myak555/EALIOR_Keyboard/Layout_Russian_Standard/ENGLISH_CAPS_Layout_Russian_Standard.png

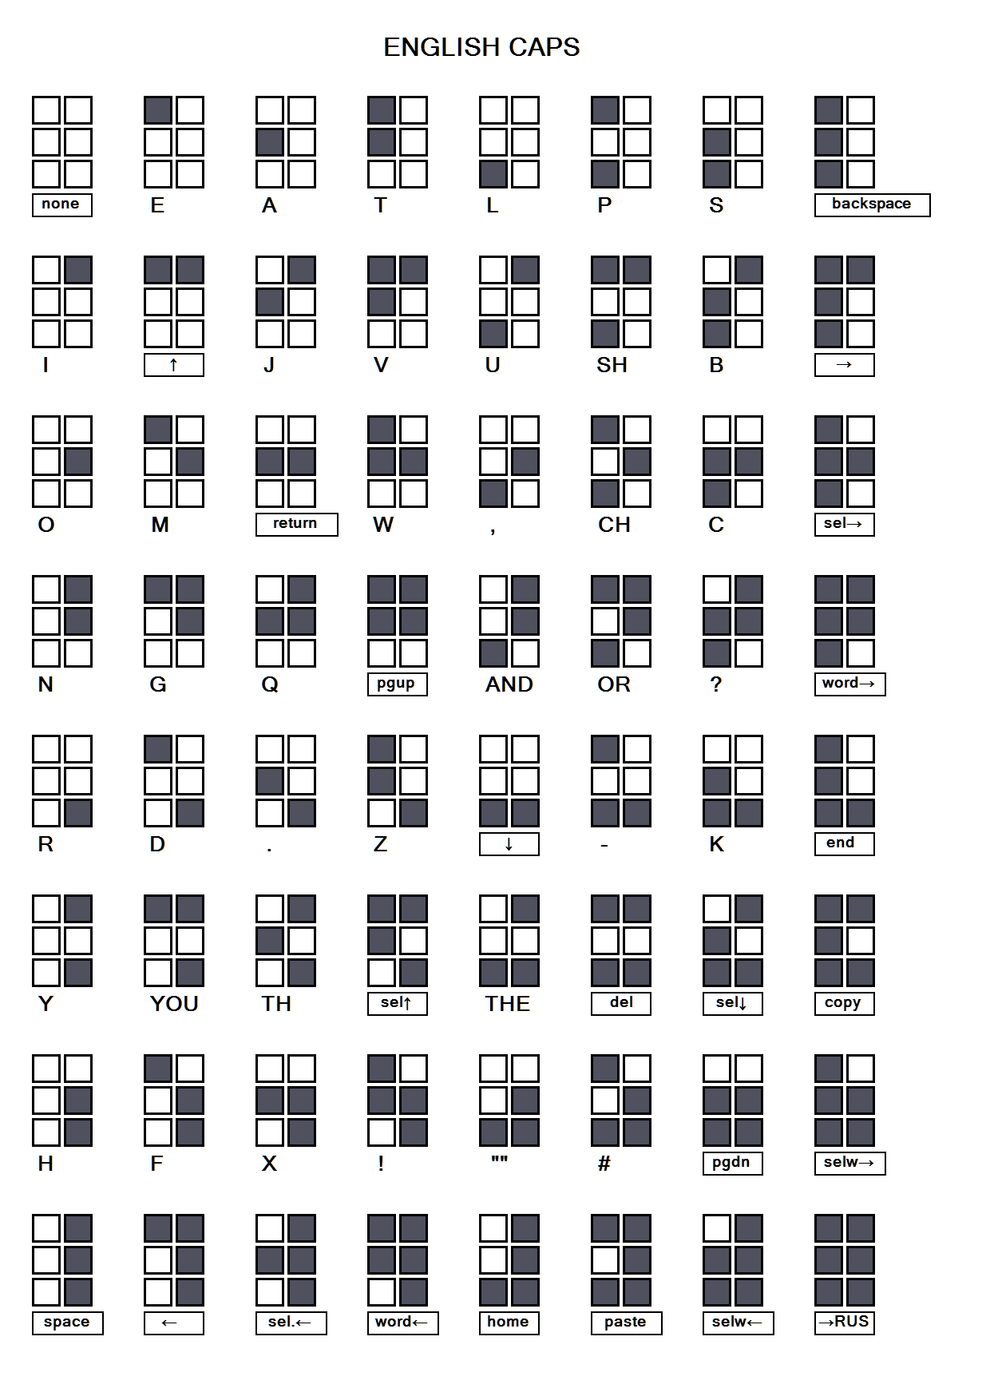
Layout_Russian_Standard/ENGLISH_CAPS_Layout_Russian_Standard.png
