myak555/EALIOR_Keyboard/Layout_Russian_Standard/RUSSIAN_NORMAL_Layout_Russian_Standard.png

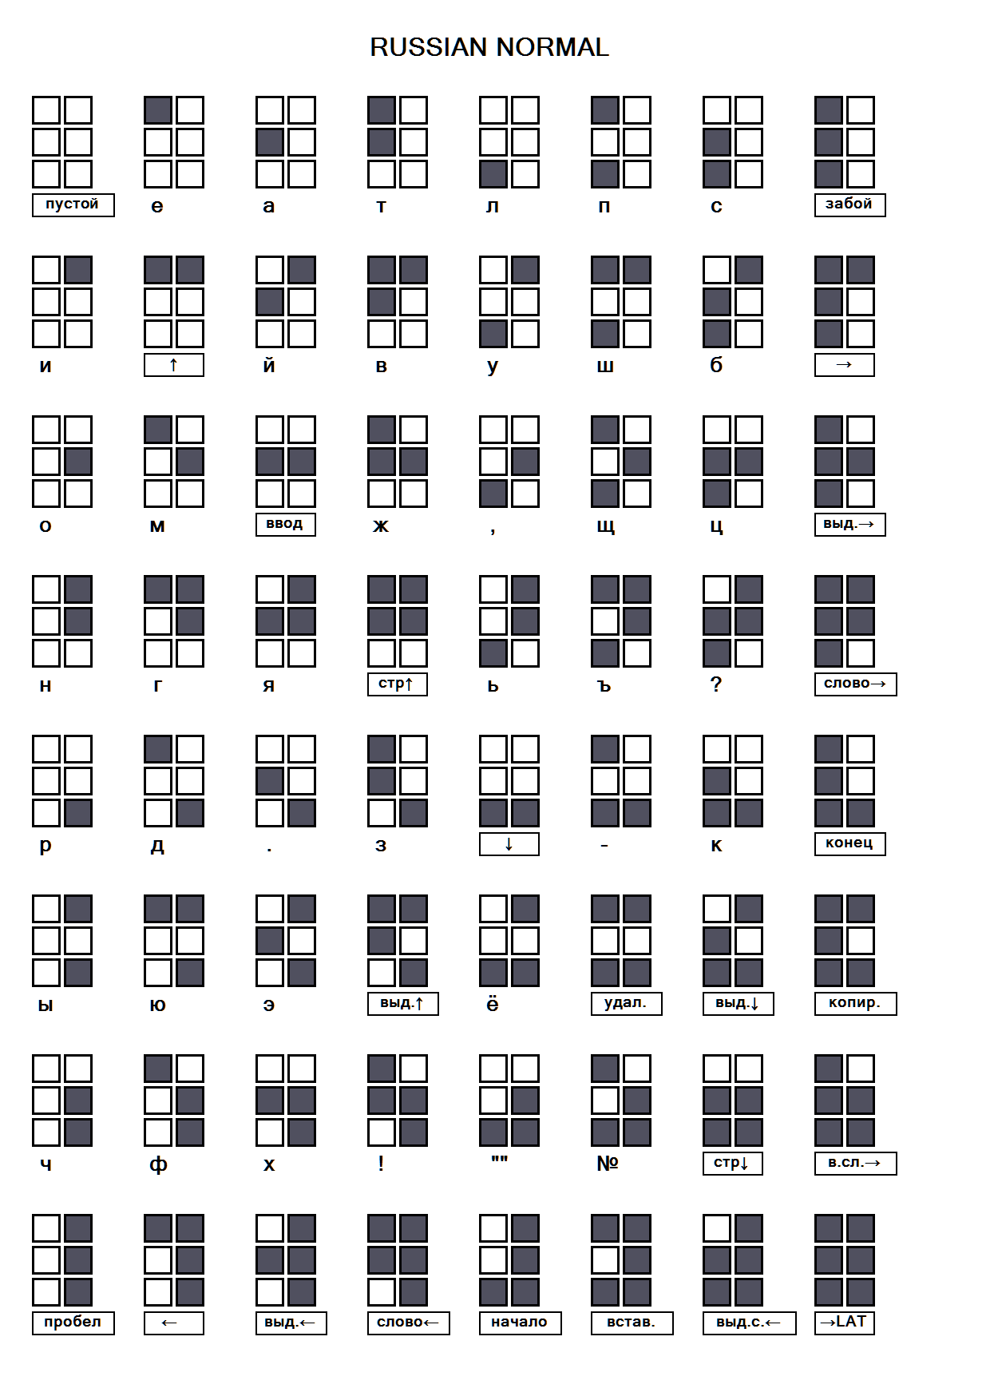
Layout_Russian_Standard/RUSSIAN_NORMAL_Layout_Russian_Standard.png
