myak555/EALIOR_Keyboard/keymapRusStandard.h

const byte _EALIOR_Mantras[] PROGMEM = {
	0x00,0x65,0x00,0x61,0x00,0x74,0x00,0x6c,0x00,0x70,0x00,0x73,0x00,0xb2,0x00,0x69,0x00,0xda,0x00,0x6a,
	0x00,0x76,0x00,0x75,0x00,0x73,0x68,0x00,0x62,0x00,0xd7,0x00,0x6f,0x00,0x6d,0x00,0xb0,0x00,0x77,0x00,
	0x2c,0x0c,0x20,0x00,0x63,0x68,0x00,0x63,0x00,0x81,0xd7,0x0f,0x00,0x6e,0x00,0x67,0x00,0x71,0x00,0xd3,
	0x00,0x61,0x6e,0x64,0x00,0x6f,0x72,0x00,0x02,0x3f,0x0c,0x20,0x00,0x80,0xd7,0x0f,0x00,0x02,0x2e,0x0c,
	0x20,0x00,0x7a,0x00,0xd9,0x00,0x2d,0x00,0x6b,0x00,0xd5,0x00,0x79,0x00,0x79,0x6f,0x75,0x00,0x74,0x68,
	0x00,0x81,0xda,0x0f,0x00,0x74,0x68,0x65,0x00,0xd4,0x00,0x81,0xd9,0x0f,0x00,0x80,0x63,0x0f,0x00,0x66,
	0x00,0x78,0x00,0x02,0x21,0x0c,0x20,0x00,0x22,0x22,0x0c,0xd8,0x00,0x23,0x00,0xd6,0x00,0x80,0x81,0xd7,
	0x0f,0x00,0x81,0xd8,0x0f,0x00,0x80,0xd8,0x0f,0x00,0xd2,0x00,0x80,0x76,0x0f,0x00,0x80,0x81,0xd8,0x0f,
	0x00,0x0b,0x06,0x00,0x01,0x45,0x00,0x01,0x41,0x00,0x01,0x54,0x00,0x01,0x4c,0x00,0x01,0x50,0x00,0x01,
	0x53,0x00,0x01,0x49,0x00,0x01,0x4a,0x00,0x01,0x56,0x00,0x01,0x55,0x00,0x01,0x53,0x68,0x00,0x01,0x42,
	0x00,0x01,0x4f,0x00,0x01,0x4d,0x00,0x01,0x57,0x00,0x01,0x3b,0x0c,0x20,0x00,0x01,0x43,0x68,0x00,0x01,
	0x43,0x00,0x01,0x4e,0x00,0x01,0x47,0x00,0x01,0x51,0x00,0x01,0x41,0x6e,0x64,0x00,0x01,0x4f,0x72,0x00,
	0x01,0x52,0x00,0x01,0x44,0x00,0x01,0x3a,0x0c,0x20,0x00,0x01,0x5a,0x00,0x01,0x5f,0x00,0x01,0x4b,0x00,
	0x01,0x59,0x00,0x01,0x59,0x6f,0x75,0x00,0x01,0x54,0x68,0x00,0x01,0x54,0x68,0x65,0x00,0x01,0x48,0x00,
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
	0x00,0x58,0x01,0x01,0x01,0x02,0x01,0x5f,0x01,0x60,0x00,0x42,0x02,0x7c,0x00,0xf1,0x02,0xd6,0x01,0x60,
	0x00,0x5a,0x00,0x5a,0x00,0x5a,0x00,0x5a,0x00,0x5a,0x00,0x5a,0x00,0x5a,0x00,0x5a,0x00,0x5a,0x00,0x5a,
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
