myak555/EALIOR_Keyboard/characters.h

/////////////////////////////////////////////////////////
//
//  EALIOR - 8-key chorded keyboard for tablets
//  Copyright (c) 2020 Mike Yakimov.  All rights reserved.
//  See main file for the license
//
//////////////////////////////////////////////////////////

#define _SHIFTMODE_LAT_NORMAL  0
#define _SHIFTMODE_LAT_SHIFTED 1 
#define _SHIFTMODE_LAT_CAPS    2  
#define _SHIFTMODE_LAT_NUMS    3
#define _SHIFTMODE_LAT_NUMLOCK 4
#define _SHIFTMODE_RUS_NORMAL  5
#define _SHIFTMODE_RUS_SHIFTED 6 
#define _SHIFTMODE_RUS_CAPS    7  
#define _SHIFTMODE_RUS_NUMS    8
#define _SHIFTMODE_RUS_NUMLOCK 9

// additional definitions of EALIOR
#define _NUL_                   0x00
#define _MODE0_                 0x01
#define _MODE1_                 0x02
#define _MODE2_                 0x03
#define _MODE3_                 0x04
#define _MODE4_                 0x05
#define _MODE5_                 0x06
#define _MODE6_                 0x07
#define _MODE7_                 0x08
#define _MODE8_                 0x09
#define _MODE9_                 0x0A
#define _RUSLAT_                0x0B
#define _DELAY_                 0x0C
#define _DISABLE_               0x0D
#define _ENABLE_                0x0E
#define _RELEASE_               0x0F

// stanadard Arduino definitions
#define _LEFT_CTRL_             0x80
#define _LEFT_SHIFT_            0x81
#define _LEFT_ALT_              0x82
#define _LEFT_GUI_              0x83
#define _RIGHT_CTRL_            0x84
#define _RIGHT_SHIFT_           0x85
#define _RIGHT_ALT_             0x86
#define _RIGHT_GUI_             0x87
#define _UP_ARROW_              0xda
#define _DOWN_ARROW_            0xd9
#define _LEFT_ARROW_            0xd8
#define _RIGHT_ARROW_           0xd7
#define _BACKSPACE_             0xb2
#define _TAB_                   0xb3
#define _RETURN_                0xb0
#define _ESC_                   0xb1
#define _INSERT_                0xd1
#define _DELETE_                0xd4
#define _PAGE_UP_               0xd3
#define _PAGE_DOWN_             0xd6
#define _HOME_                  0xd2
#define _END_                   0xd5
#define _CAPS_LOCK_             0xc1
#define _F1_                    0xc2
#define _F2_                    0xc3
#define _F3_                    0xc4
#define _F4_                    0xc5
#define _F5_                    0xc7
#define _F7_                    0xc8
#define _F8_                    0xc9
#define _F9_                    0xca
#define _F10_                   0xcb
#define _F11_                   0xcc
#define _F12_                   0xcd
